Dept-Advanced-Computing-Sciences/CoRoSect/Robot Extension/technical_drawings_and_STEP/DOF 1 Guide Rail/DOF1 Motor Shaft 6mm.step

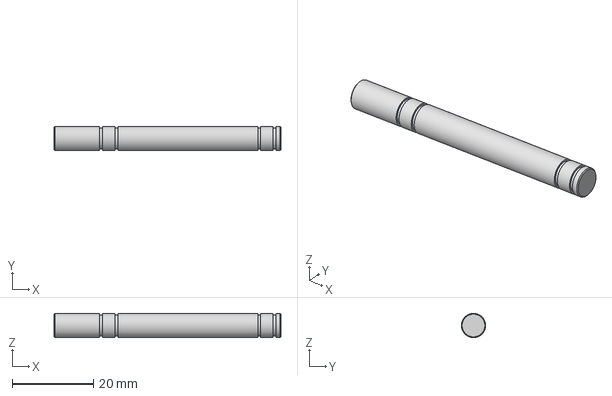
[picture p15: CAD file, 2025-05-28]
Robot Extension/technical_drawings_and_STEP/DOF 1 Guide Rail/DOF1 Motor Shaft 6mm.step
56.0 x 5.99 x 6.00 mm
