Dept-Advanced-Computing-Sciences/CoRoSect/Robot Extension/technical_drawings_and_STEP/DOF 2/Adapter Plate SpurGear-Base Plate.step

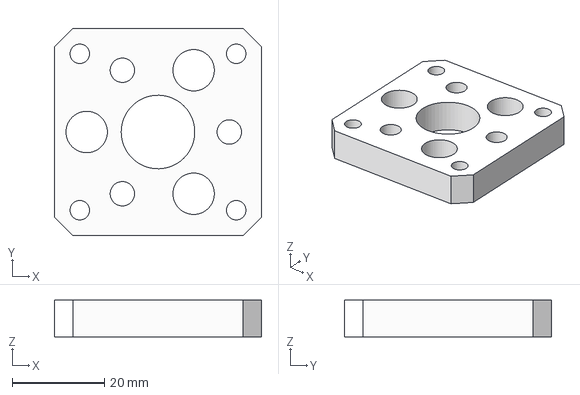
[picture p16: CAD file, 2025-05-28]
Robot Extension/technical_drawings_and_STEP/DOF 2/Adapter Plate SpurGear-Base Plate.step
45.0 x 45.0 x 8.00 mm
