Dept-Advanced-Computing-Sciences/CoRoSect/scripts/reachability_simulation/urdf/meshes/iiwa14/collision/link_6.stl

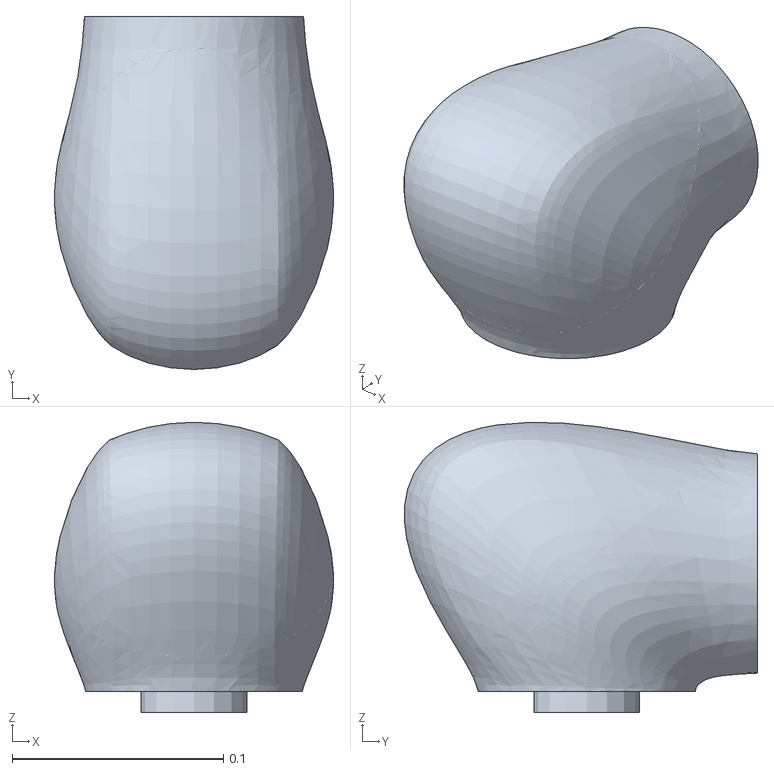
[picture p17: CAD file, 2025-05-28]
scripts/reachability_simulation/urdf/meshes/iiwa14/collision/link_6.stl
0.132 x 0.167 x 0.138
