Dept-Advanced-Computing-Sciences/CoRoSect/scripts/reachability_simulation/urdf/meshes/iiwa14/visual/link_4.stl

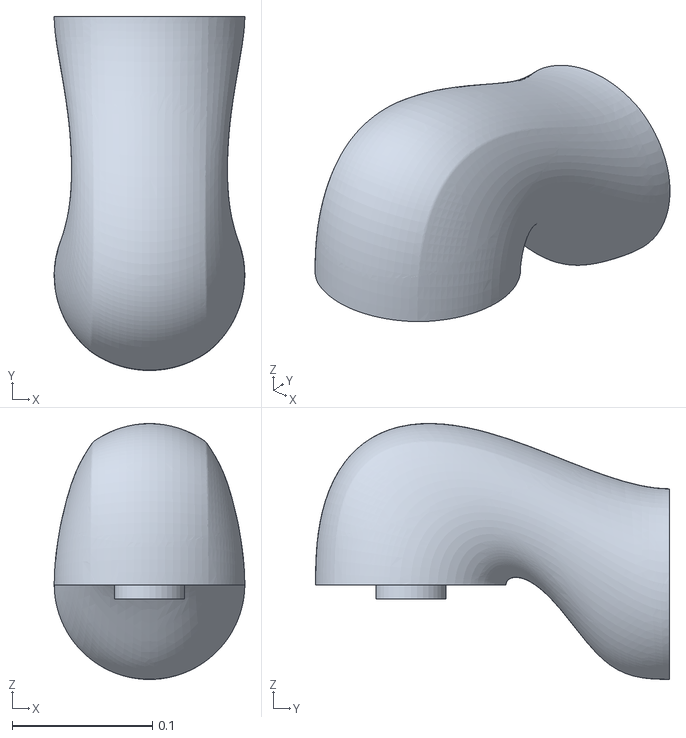
[picture p18: CAD file, 2025-05-28]
scripts/reachability_simulation/urdf/meshes/iiwa14/visual/link_4.stl
0.136 x 0.252 x 0.183
