Dept-Advanced-Computing-Sciences/CoRoSect/Robot Extension/technical_drawings_and_STEP/DOF 1 Guide Rail/DOF1 CPM Mounting Plate.step

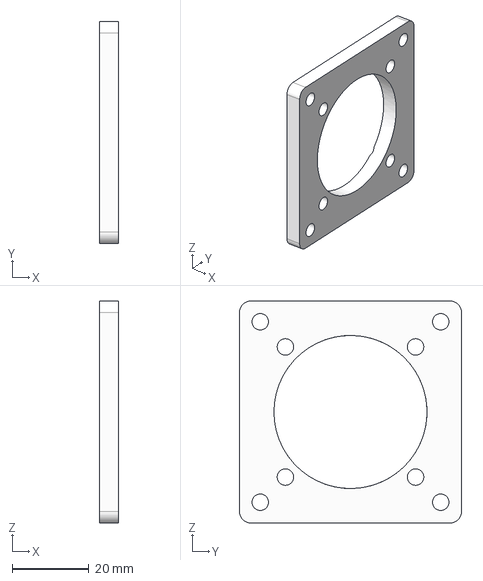
[picture p19: CAD file, 2025-05-28]
Robot Extension/technical_drawings_and_STEP/DOF 1 Guide Rail/DOF1 CPM Mounting Plate.step
5.00 x 58.0 x 58.0 mm
