Dept-Advanced-Computing-Sciences/CoRoSect/Robot Extension/technical_drawings_and_STEP/DOF 2/Base Plate 2DOF.step

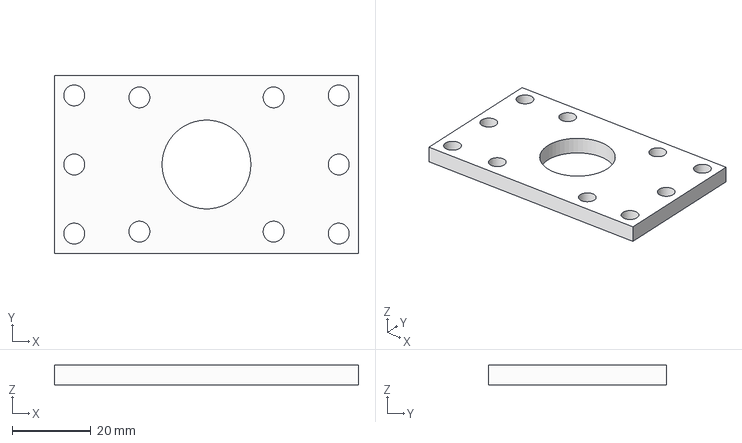
[picture p20: CAD file, 2025-05-28]
Robot Extension/technical_drawings_and_STEP/DOF 2/Base Plate 2DOF.step
77.0 x 45.0 x 5.00 mm
