Dept-Advanced-Computing-Sciences/CoRoSect/scripts/reachability_simulation/urdf/meshes/iiwa14/collision/kuka_flange.stl

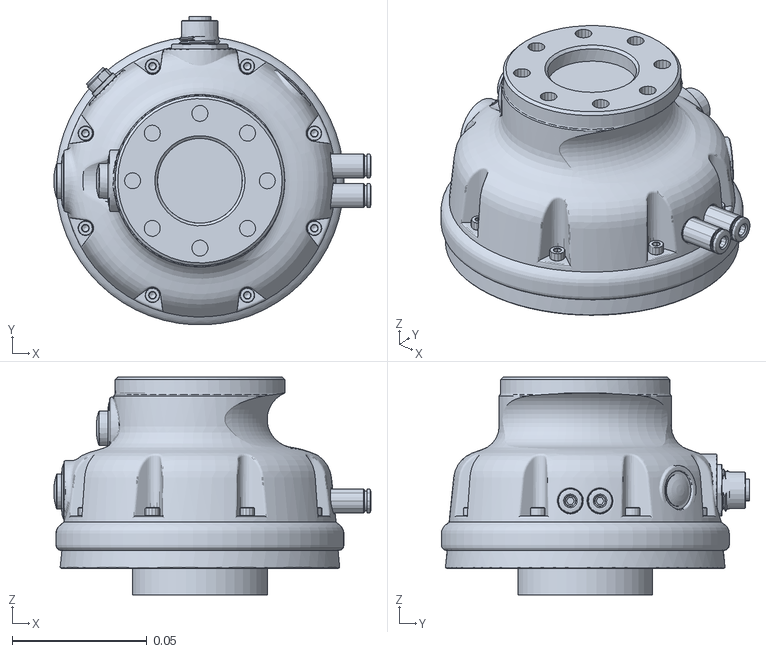
[picture p21: CAD file, 2025-05-28]
scripts/reachability_simulation/urdf/meshes/iiwa14/collision/kuka_flange.stl
0.118 x 0.114 x 0.0809
