Dept-Advanced-Computing-Sciences/CoRoSect/scripts/reachability_simulation/urdf/meshes/Linear Drive Sept2023/2 DOF.stl

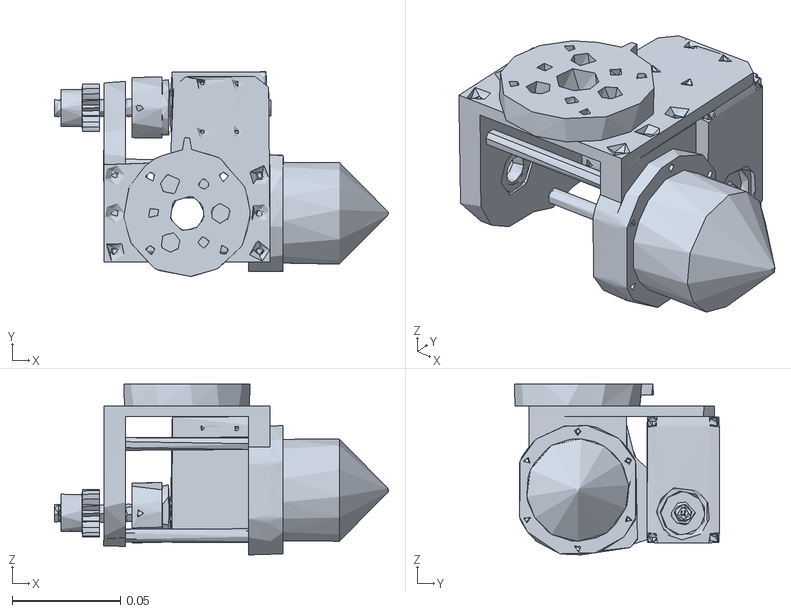
[picture p22: CAD file, 2025-05-28]
scripts/reachability_simulation/urdf/meshes/Linear Drive Sept2023/2 DOF.stl
0.155 x 0.0948 x 0.079
