Dept-Advanced-Computing-Sciences/CoRoSect/Robot Extension/technical_drawings_and_STEP/DOF 1 Guide Rail/Rail-Kuka Connector Plate.step

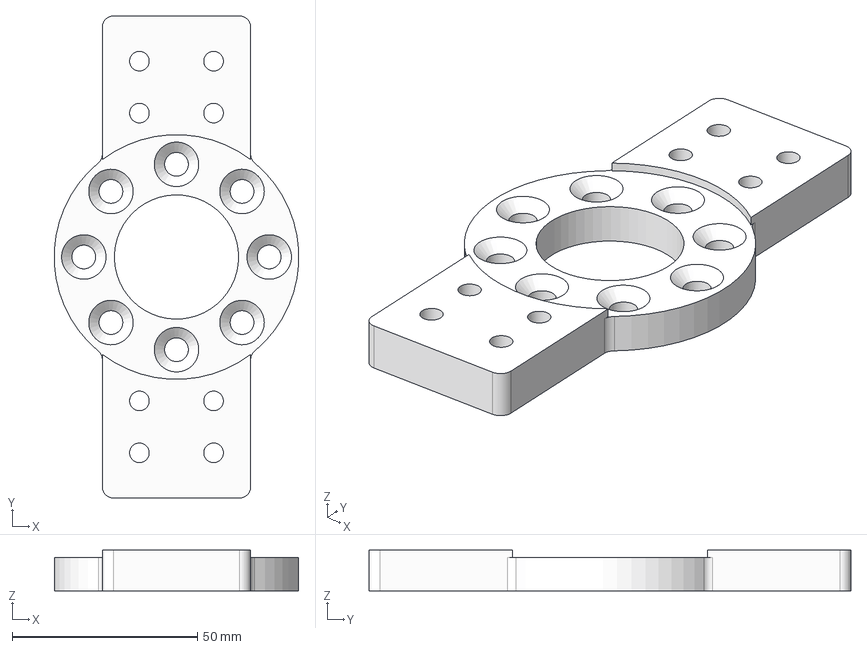
[picture p23: CAD file, 2025-05-28]
Robot Extension/technical_drawings_and_STEP/DOF 1 Guide Rail/Rail-Kuka Connector Plate.step
65.9 x 130.0 x 11.0 mm
