Dept-Advanced-Computing-Sciences/CoRoSect/Robot Extension/technical_drawings_and_STEP/DOF 2/Break Mount 2DOF.step

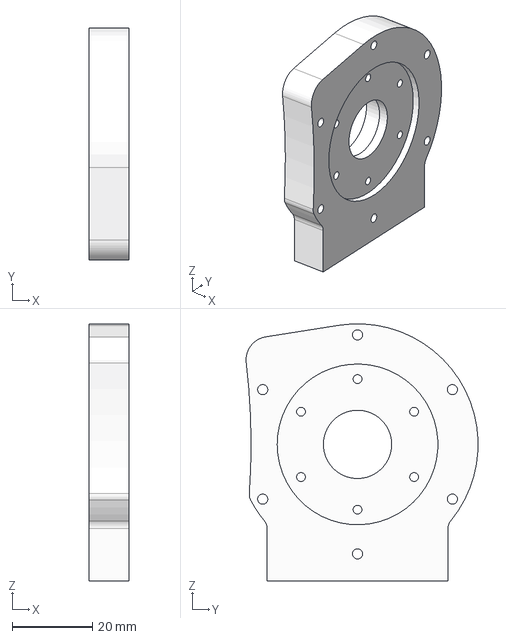
[picture p24: CAD file, 2025-05-28]
Robot Extension/technical_drawings_and_STEP/DOF 2/Break Mount 2DOF.step
10.0 x 57.7 x 64.0 mm
