Dept-Advanced-Computing-Sciences/CoRoSect/Robot Extension/technical_drawings_and_STEP/DOF 1 Guide Rail/DOF1 Shaft Mount.step

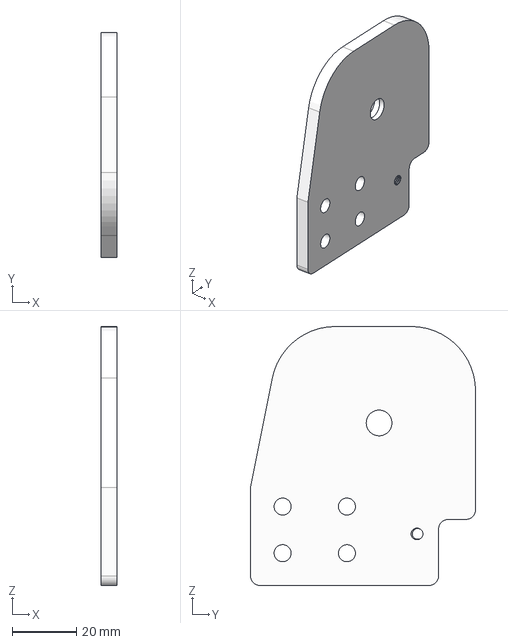
[picture p25: CAD file, 2025-05-28]
Robot Extension/technical_drawings_and_STEP/DOF 1 Guide Rail/DOF1 Shaft Mount.step
5.00 x 70.0 x 80.5 mm
