Dept-Advanced-Computing-Sciences/CoRoSect/scripts/reachability_simulation/urdf/meshes/iiwa14/visual/link_7.stl

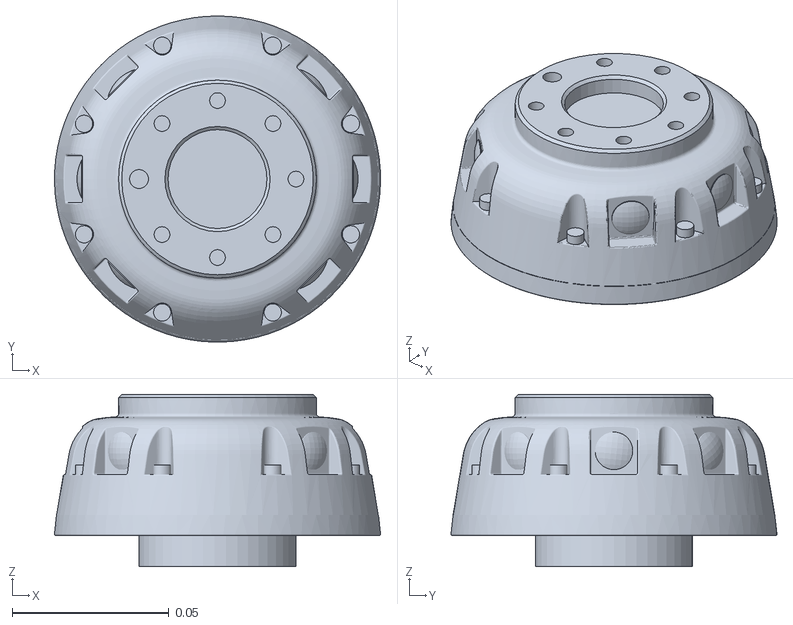
[picture p26: CAD file, 2025-05-28]
scripts/reachability_simulation/urdf/meshes/iiwa14/visual/link_7.stl
0.104 x 0.104 x 0.0549
