Dept-Advanced-Computing-Sciences/CoRoSect/scripts/reachability_simulation/urdf/meshes/iiwa14/collision/link_3.stl

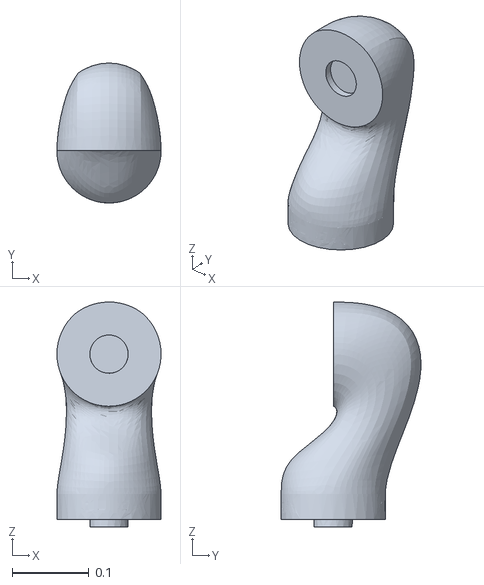
[picture p28: CAD file, 2025-05-28]
scripts/reachability_simulation/urdf/meshes/iiwa14/collision/link_3.stl
0.136 x 0.183 x 0.293
