Dept-Advanced-Computing-Sciences/CoRoSect/Robot Extension/technical_drawings_and_STEP/DOF 3/Shaft 2DOF.pdf

Ø10

Ø9.6

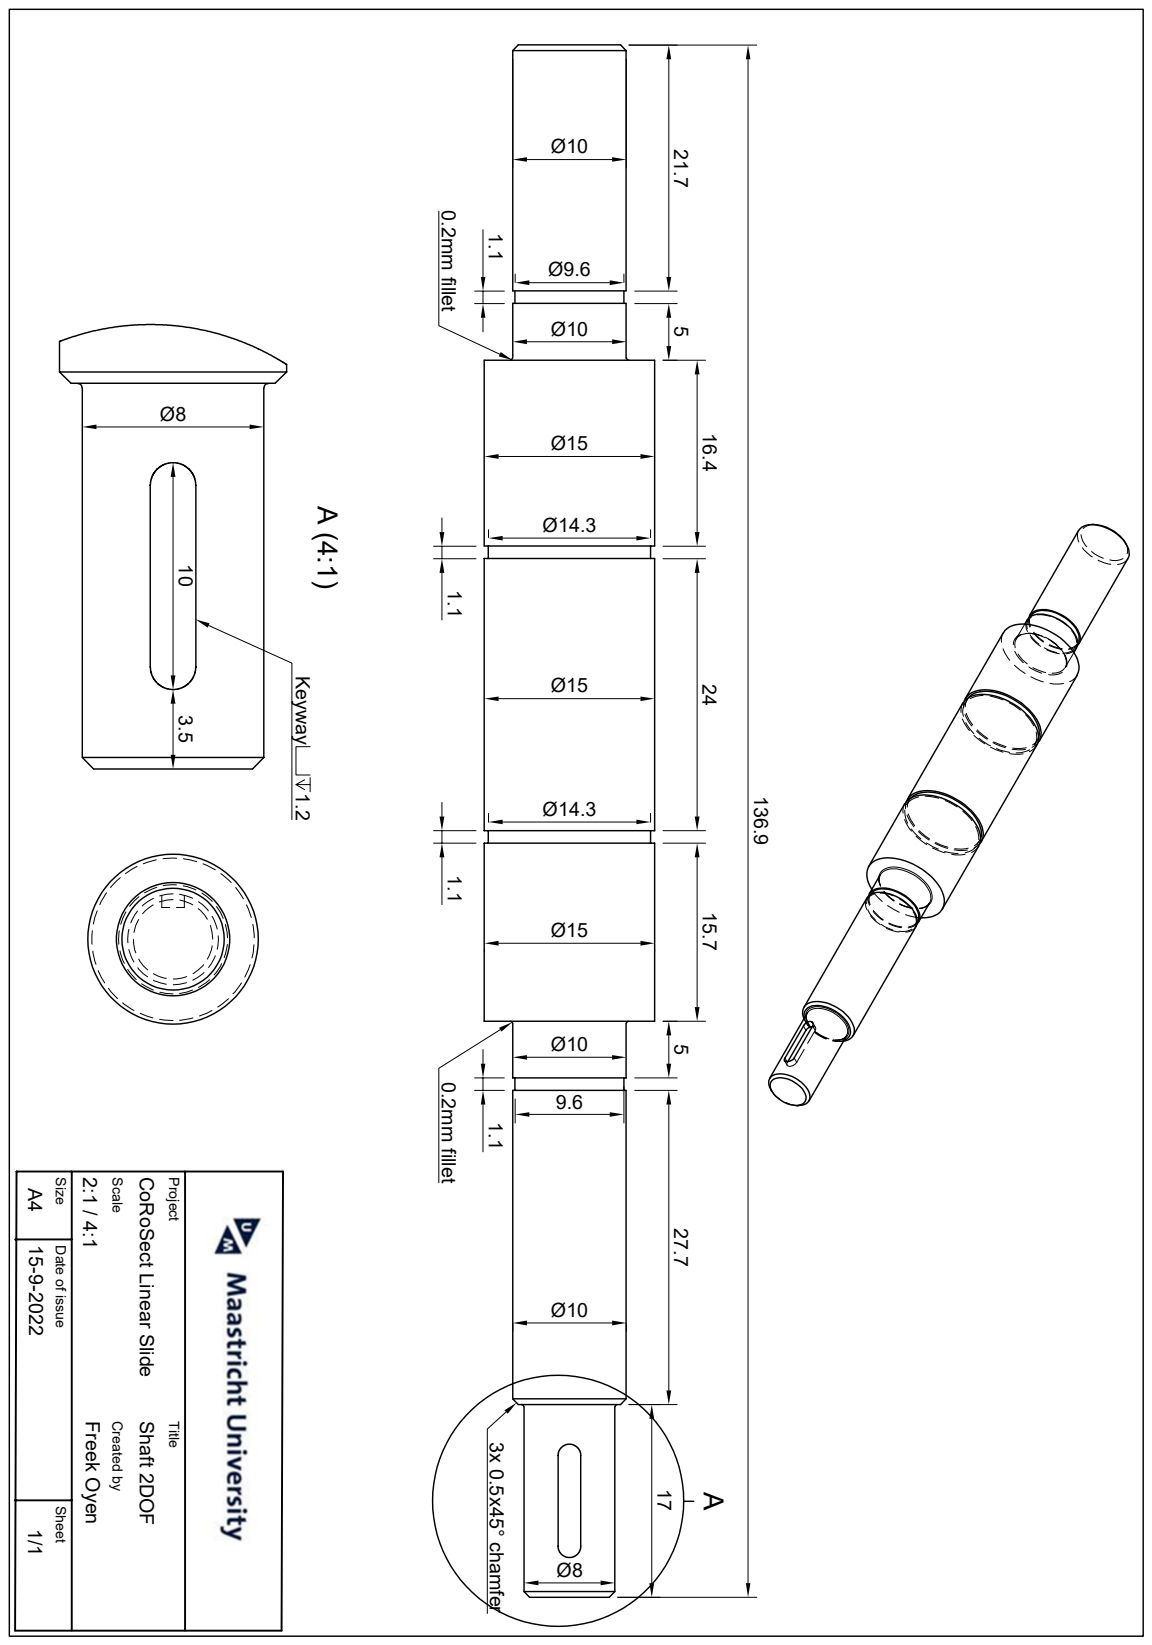
[picture p35: page 1]
1.1 1.1 3x 0.5x45° chamfer 0.2mm fillet 0.2mm fillet; Keyway 1.2

Created by Project Date of issue Sheet Size Scale Title 15-9-2022 1/1 CoRoSect Linear Slide Freek Oyen 2:1 / 4:1 A4 Shaft 2DOF 136.9 21.7 5 16.4 24 15.7 5 27.7 17
