Dept-Advanced-Computing-Sciences/CoRoSect/Robot Extension/technical_drawings_and_STEP/DOF 3/Adapter Plate RG6-Shaft.pdf

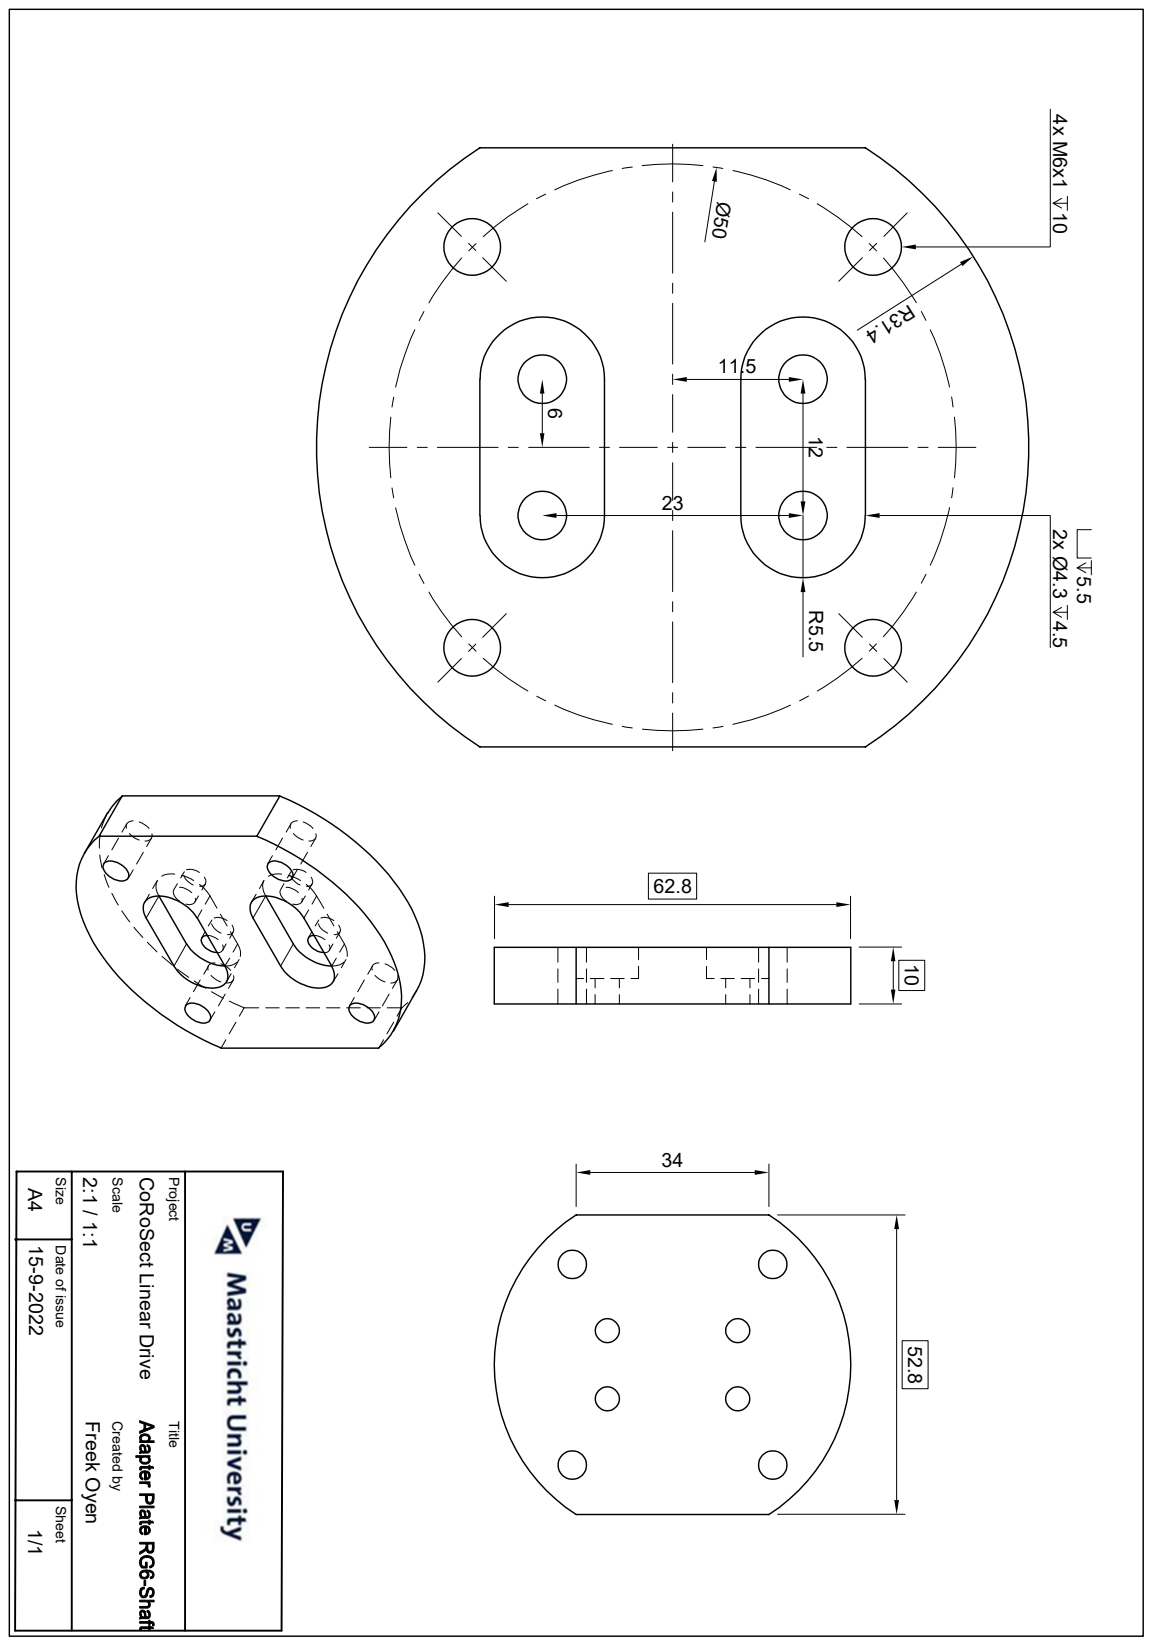
[picture p42: page 1]

Created by Project Date of issue Sheet Size Scale Title 15-9-2022 1/1 CoRoSect Linear Drive Freek Oyen 2:1 / 1:1 A4 52.8 10
